ExploreEmbedded/Hornbill-ESP32-DEV/Others/images/04.JPG

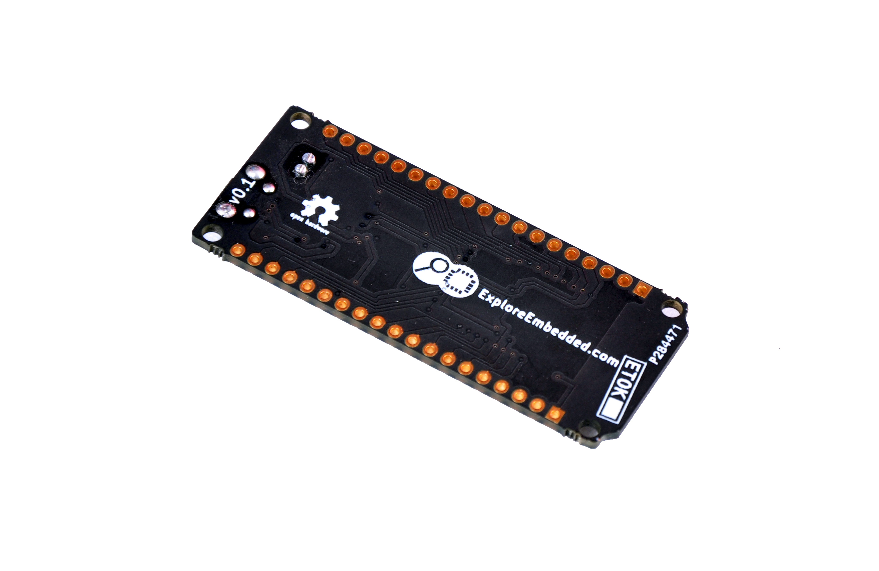
Others/images/04.JPG
