ExploreEmbedded/Hornbill-ESP32-DEV/pinout/pre version/pinout_horbill.jpg

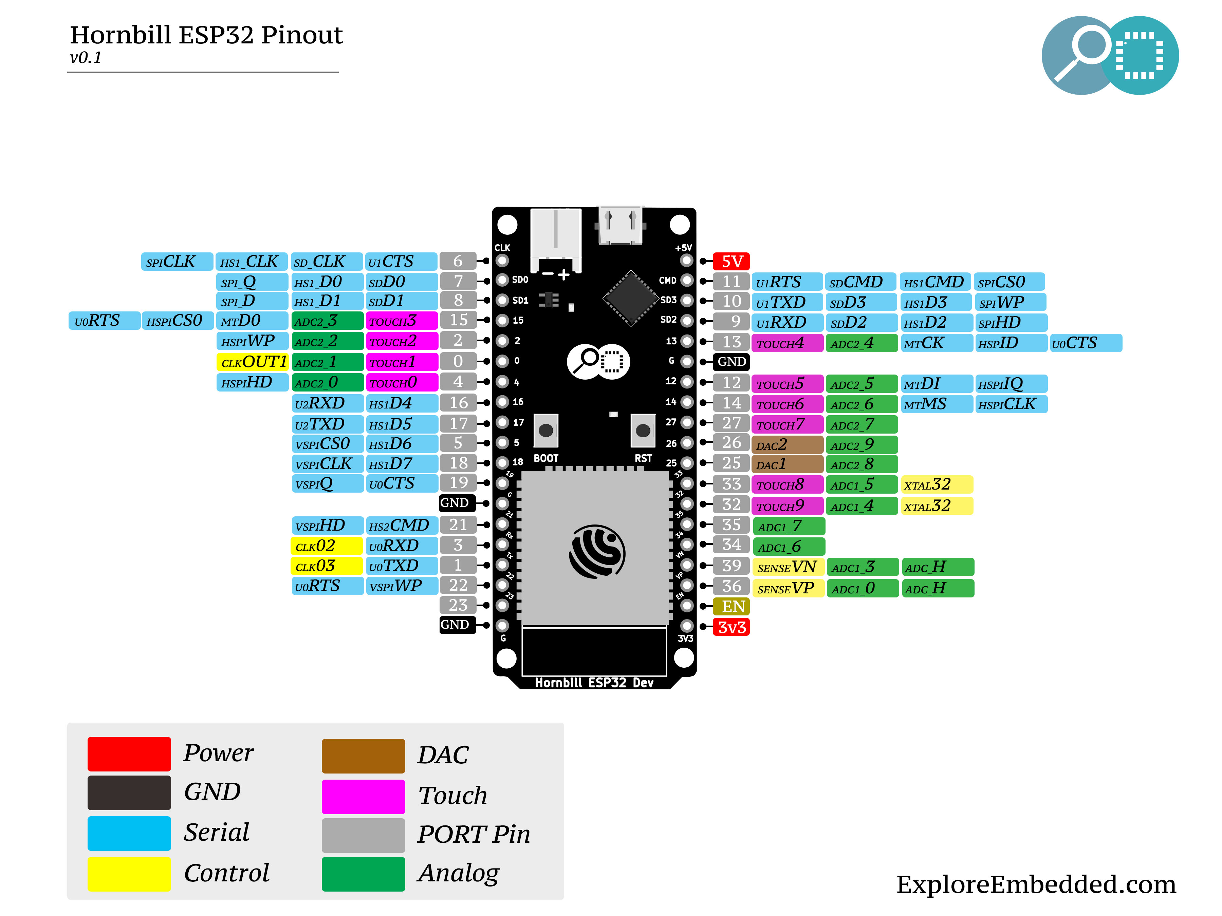
pinout/pre version/pinout_horbill.jpg
